FOSH-following-demand/Flow-Through-Colorimeter/software/test_Led_dimmer/test_Led_dimmer.ino

#include <Wire.h>
#include "Adafruit_TCS34725.h"

/* TCS34725 */
/* Connect SCL    to analog 5
   Connect SDA    to analog 4
   Connect VDD    to 3.3V DC
   Connect GROUND to common ground */

/* Initialise with default values (int time = 2.4ms, gain = 1x) */
// Adafruit_TCS34725 tcs = Adafruit_TCS34725();

/* Initialise with specific int time and gain values */
Adafruit_TCS34725 tcs = Adafruit_TCS34725(TCS34725_INTEGRATIONTIME_700MS, TCS34725_GAIN_1X);

void setup(){
 Serial.begin(115200);
 
 if (tcs.begin()) {
    Serial.println("Found sensor");
  } else {
    Serial.println("No TCS34725 found ... check your connections");
    while (1);
  }
}

void loop(){
  uint16_t r, g, b, c, colorTemp, lux;

  for( int i=0; i<256; i+=1 ){
   analogWrite(3, i);
   Serial.println(i);
   delay(500);
   tcs.getRawData(&r, &g, &b, &c);
   Serial.print("R: "); Serial.print(r, DEC); Serial.print(" ");
   Serial.print("G: "); Serial.print(g, DEC); Serial.print(" ");
   Serial.print("B: "); Serial.print(b, DEC); Serial.print(" ");
  Serial.print("C: "); Serial.print(c, DEC); Serial.print(" ");
  Serial.println(" ");
  }
}
